martin-77/Samsung_Stand/cad/fit_coupons/STEP/fit_outer_receiver_c050.step

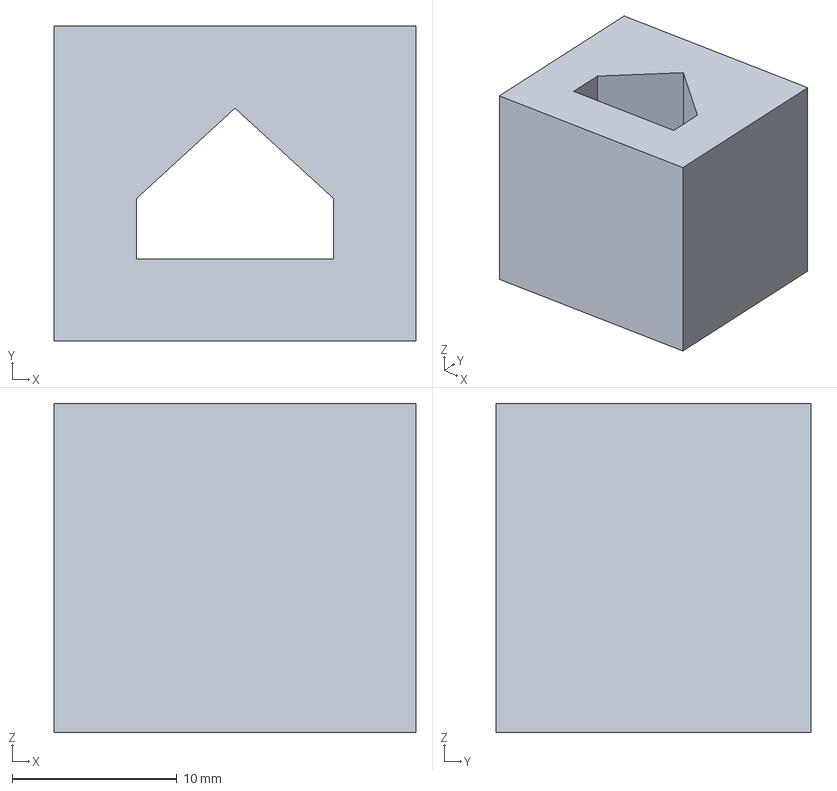
[picture p15: CAD file, 2026-09-20]
cad/fit_coupons/STEP/fit_outer_receiver_c050.step
22.0 x 19.1 x 20.0 mm
