martin-77/Samsung_Stand/cad/retainer_coupons/STEP/retainer_coupon_joint_pin.step

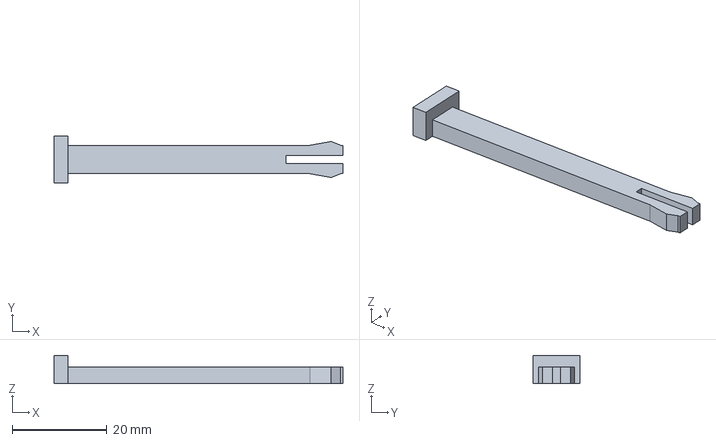
[picture p16: CAD file, 2026-09-20]
cad/retainer_coupons/STEP/retainer_coupon_joint_pin.step
61.0 x 10.0 x 6.00 mm
