martin-77/Samsung_Stand/cad/v8/STEP/samsung_stand_v8_track_wear_arc.step

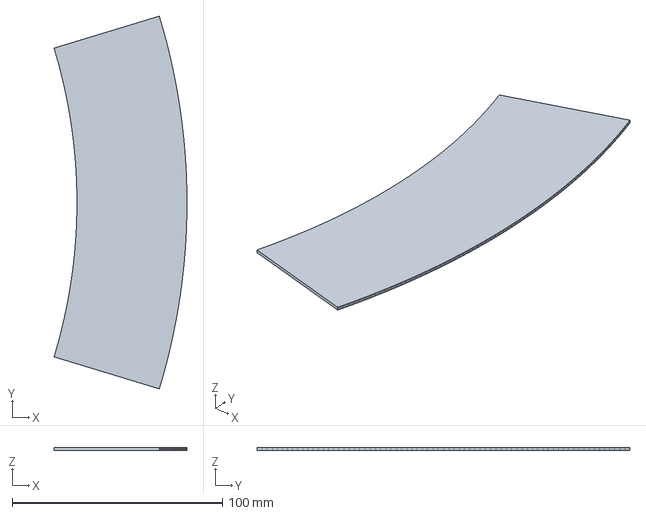
[picture p17: CAD file, 2026-09-20]
cad/v8/STEP/samsung_stand_v8_track_wear_arc.step
63.3 x 177.4 x 1.20 mm
