martin-77/Samsung_Stand/cad/fit_coupons/STEP/fit_base_receiver_c030.step

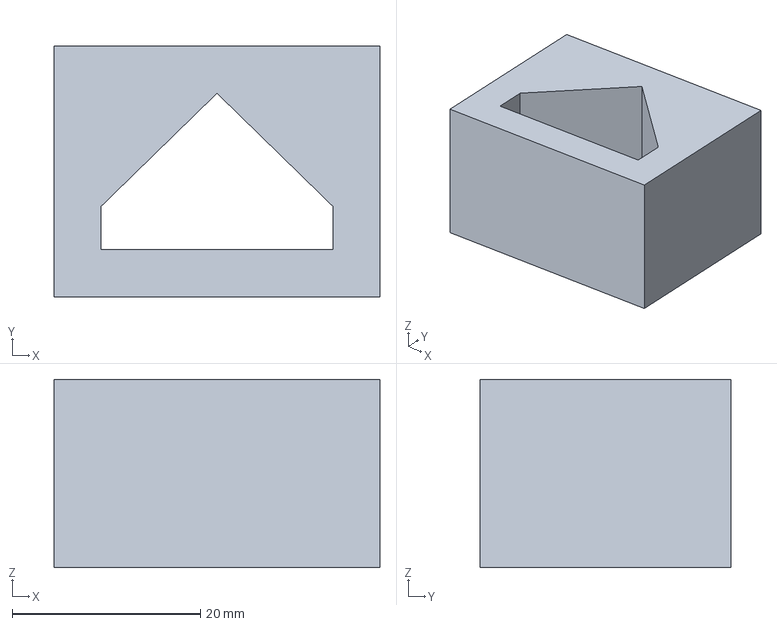
[picture p18: CAD file, 2026-09-20]
cad/fit_coupons/STEP/fit_base_receiver_c030.step
34.6 x 26.6 x 20.0 mm
