martin-77/Samsung_Stand/cad/v8/STEP/samsung_stand_v8_inner_arm.step

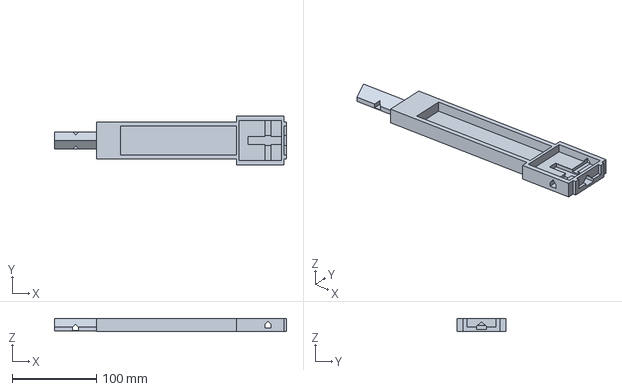
[picture p19: CAD file, 2026-09-20]
cad/v8/STEP/samsung_stand_v8_inner_arm.step
275.0 x 58.0 x 15.0 mm
