martin-77/Samsung_Stand/cad/fit_coupons/STEP/fit_inner_receiver_c030.step

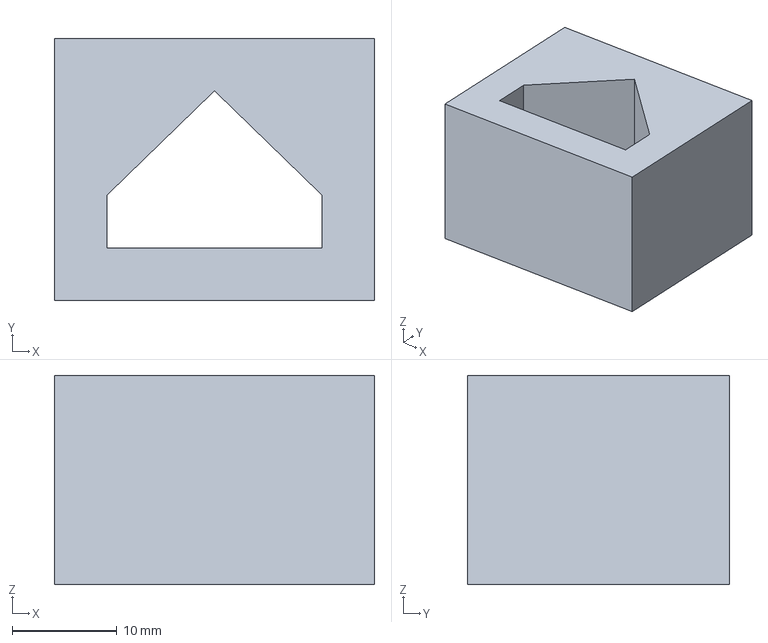
[picture p20: CAD file, 2026-09-20]
cad/fit_coupons/STEP/fit_inner_receiver_c030.step
30.6 x 25.0 x 20.0 mm
