martin-77/Samsung_Stand/cad/v8/STEP/samsung_stand_v8_outer_guide.step

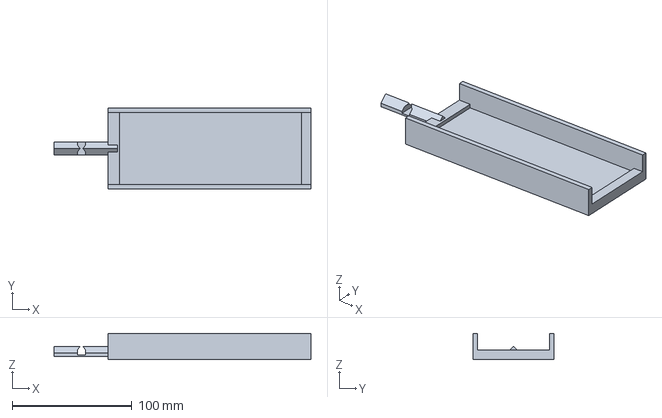
[picture p21: CAD file, 2026-09-20]
cad/v8/STEP/samsung_stand_v8_outer_guide.step
215.0 x 68.0 x 22.0 mm
