martin-77/Samsung_Stand/cad/v8/STEP/samsung_stand_v8_rotor.step

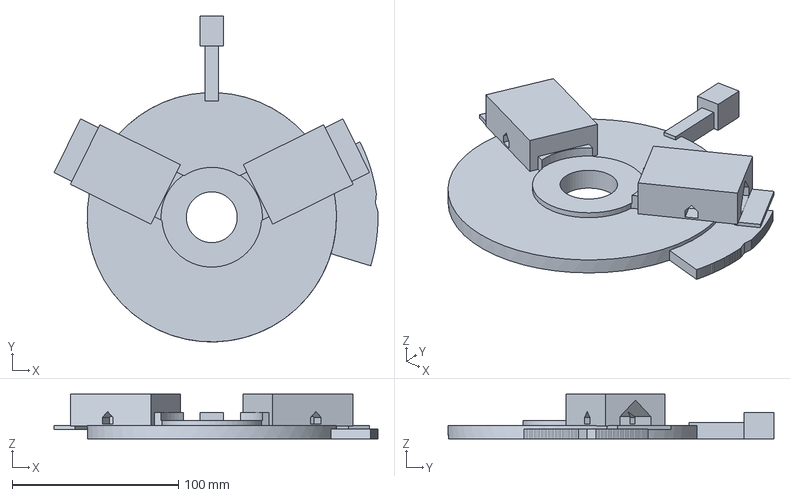
[picture p22: CAD file, 2026-09-20]
cad/v8/STEP/samsung_stand_v8_rotor.step
194.9 x 196.0 x 27.0 mm
