martin-77/Samsung_Stand/cad/fit_coupons/STEP/fit_base_male_probe.step

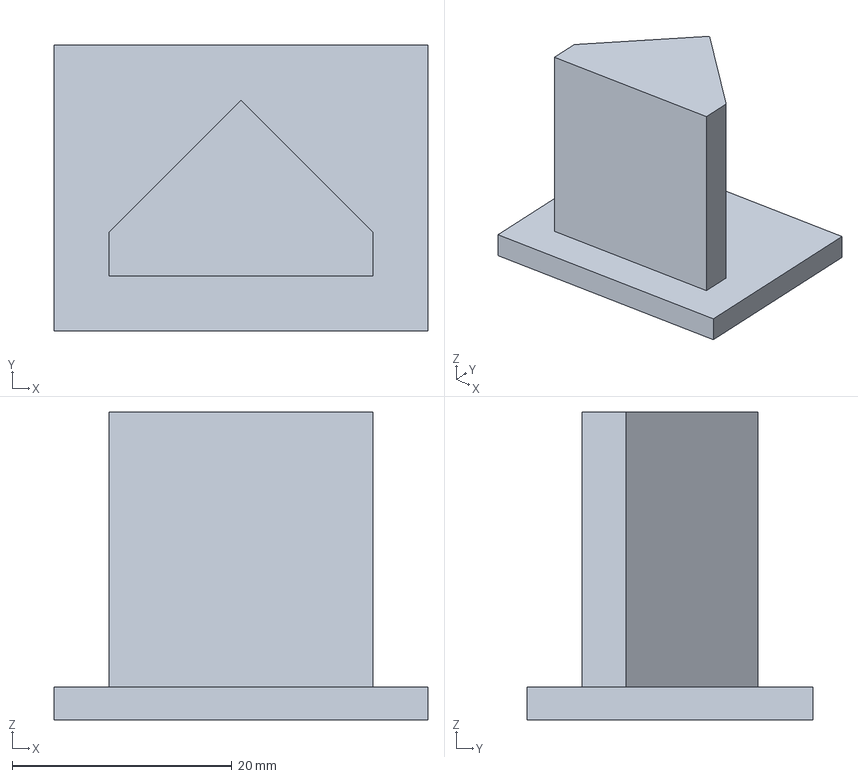
[picture p23: CAD file, 2026-09-20]
cad/fit_coupons/STEP/fit_base_male_probe.step
34.0 x 26.0 x 28.0 mm
