martin-77/Samsung_Stand/cad/v8/STEP/samsung_stand_v8_base_center.step

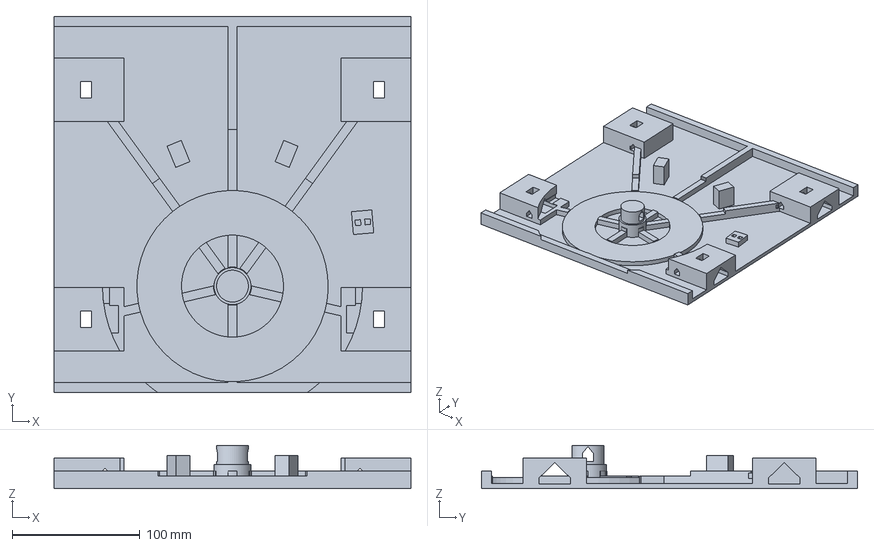
[picture p24: CAD file, 2026-09-20]
cad/v8/STEP/samsung_stand_v8_base_center.step
280.0 x 295.0 x 34.0 mm
