martin-77/Samsung_Stand/cad/v8/STEP/samsung_stand_v8_saddle_insert_blank.step

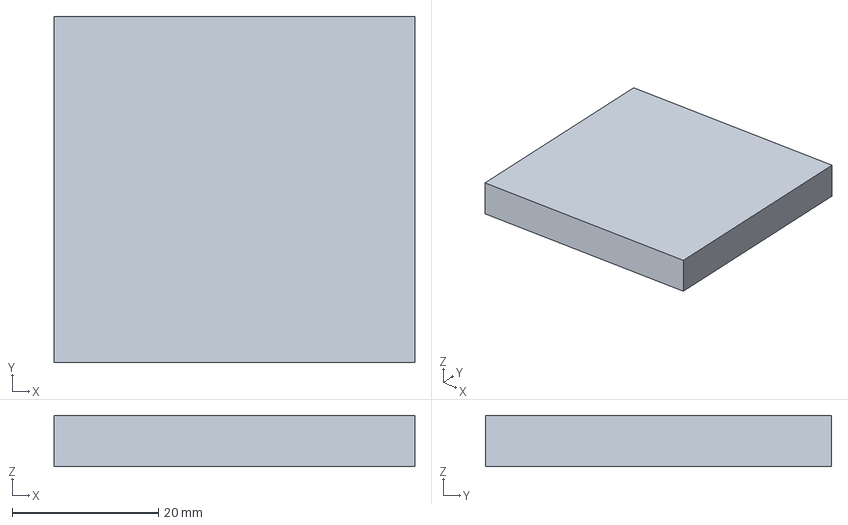
[picture p25: CAD file, 2026-09-20]
cad/v8/STEP/samsung_stand_v8_saddle_insert_blank.step
49.4 x 47.4 x 7.00 mm
