martin-77/Samsung_Stand/cad/fit_coupons/STEP/fit_outer_male_probe.step

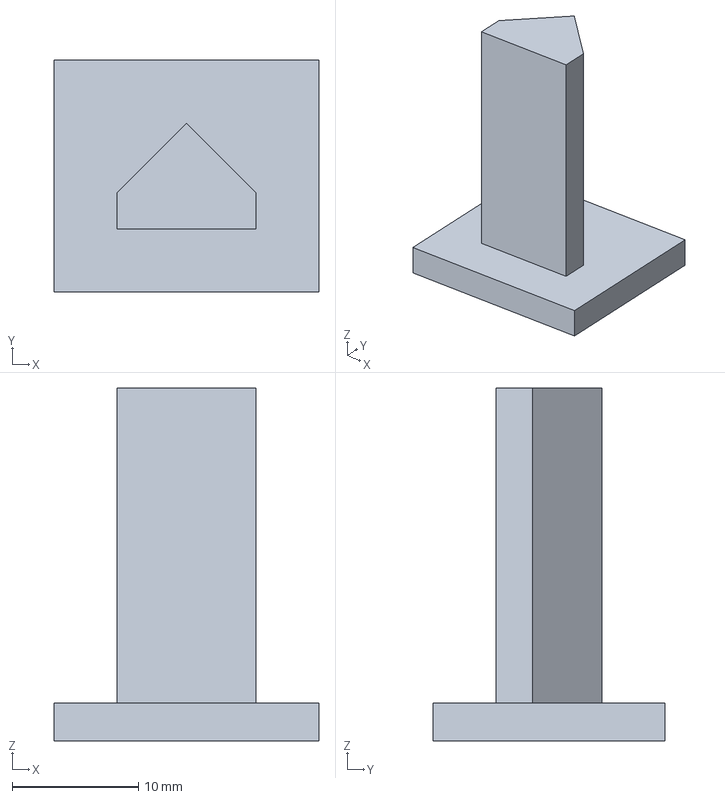
[picture p26: CAD file, 2026-09-20]
cad/fit_coupons/STEP/fit_outer_male_probe.step
21.0 x 18.4 x 28.0 mm
