martin-77/Samsung_Stand/cad/v8/STEP/samsung_stand_v8_center_wear_ring.step

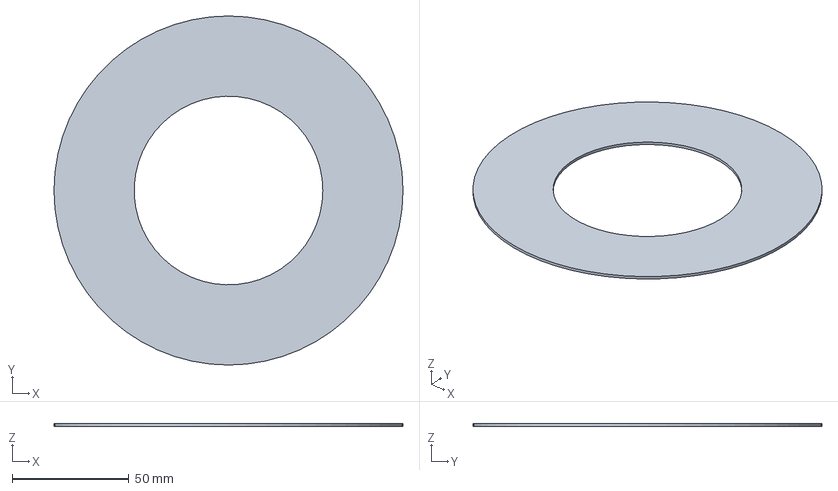
[picture p27: CAD file, 2026-09-20]
cad/v8/STEP/samsung_stand_v8_center_wear_ring.step
149.3 x 149.3 x 1.20 mm
